mdevalcourt-rgb/ECEN-404-Group-2-Capstone/Website GUI/src/OtaUpdater.cpp

#include "OtaUpdater.h"

#include <ArduinoOTA.h>
#include <Arduino.h>

void setupOTA(const char *hostname, const char *password) {
  ArduinoOTA.setHostname(hostname);
  ArduinoOTA.setPassword(password);

  ArduinoOTA.onStart([]() {
    String type = (ArduinoOTA.getCommand() == U_FLASH) ? "sketch" : "filesystem";
    Serial.println("OTA Start: updating " + type);
  });

  ArduinoOTA.onEnd([]() {
    Serial.println("\nOTA End. Rebooting...");
  });

  ArduinoOTA.onProgress([](unsigned int progress, unsigned int total) {
    Serial.printf("OTA Progress: %u%%\r", (progress * 100) / total);
  });

  ArduinoOTA.onError([](ota_error_t error) {
    Serial.printf("OTA Error[%u]: ", error);
    if      (error == OTA_AUTH_ERROR)    Serial.println("Auth Failed");
    else if (error == OTA_BEGIN_ERROR)   Serial.println("Begin Failed");
    else if (error == OTA_CONNECT_ERROR) Serial.println("Connect Failed");
    else if (error == OTA_RECEIVE_ERROR) Serial.println("Receive Failed");
    else if (error == OTA_END_ERROR)     Serial.println("End Failed");
  });

  ArduinoOTA.begin();
  Serial.println("OTA ready.");
}

void handleOTA() {
  ArduinoOTA.handle();
}
